TheLittleEngineers/27C512E-TO-2532S-V1R0/Images/png/Board.png

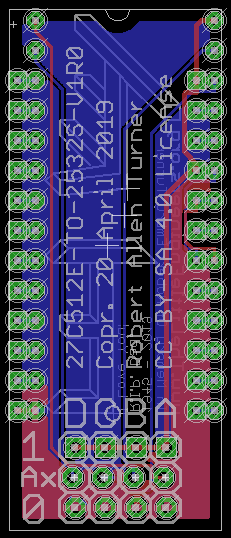
Images/png/Board.png
