TheLittleEngineers/27C512E-TO-2532S-V1R0/Images/png/Board_Bottom_ccbb43645ecdf33bebab5a3d648b6d6c.png

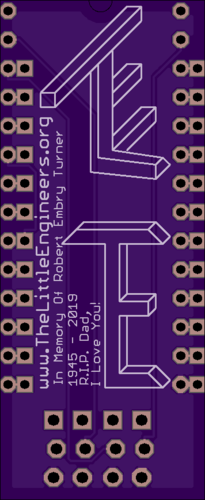
Images/png/Board_Bottom_ccbb43645ecdf33bebab5a3d648b6d6c.png
