TheLittleEngineers/27C512E-TO-2532S-V1R0/Images/png/Board_Outline_6028282c5fdcc0729c080498a5109b80.png

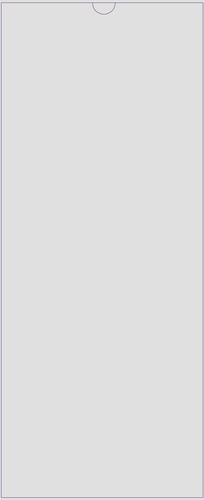
Images/png/Board_Outline_6028282c5fdcc0729c080498a5109b80.png
