TheLittleEngineers/27C512E-TO-2532S-V1R0/Images/png/Bottom_Silk_Screen_157bdbb59df11820652dcfb5b0bd4d44.png

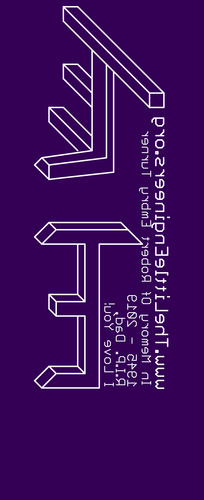
Images/png/Bottom_Silk_Screen_157bdbb59df11820652dcfb5b0bd4d44.png
