TheLittleEngineers/27C512E-TO-2532S-V1R0/Images/png/Drills_8211e1ab3b943c486193aabd76c98ad6.png

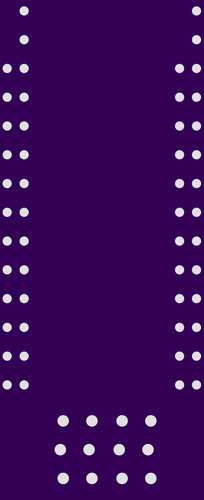
Images/png/Drills_8211e1ab3b943c486193aabd76c98ad6.png
