TheLittleEngineers/27C512E-TO-2532S-V1R0/Images/png/From_Gerbers/Top_Silk_Screen.png

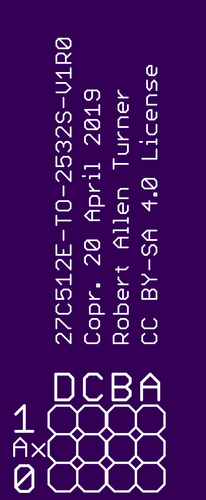
Images/png/From_Gerbers/Top_Silk_Screen.png
