TheLittleEngineers/27C512E-TO-2532S-V1R0/Images/png/Bottom_Solder_Mask_6d0ef9b1ec51710361c40d50df8ff29c.png

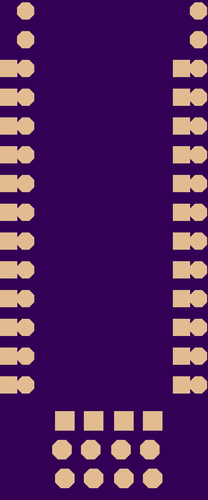
Images/png/Bottom_Solder_Mask_6d0ef9b1ec51710361c40d50df8ff29c.png
